islandmagic/bb-link/enclosure/contribs/F4LFJ/BB-Link_case_02.jpeg

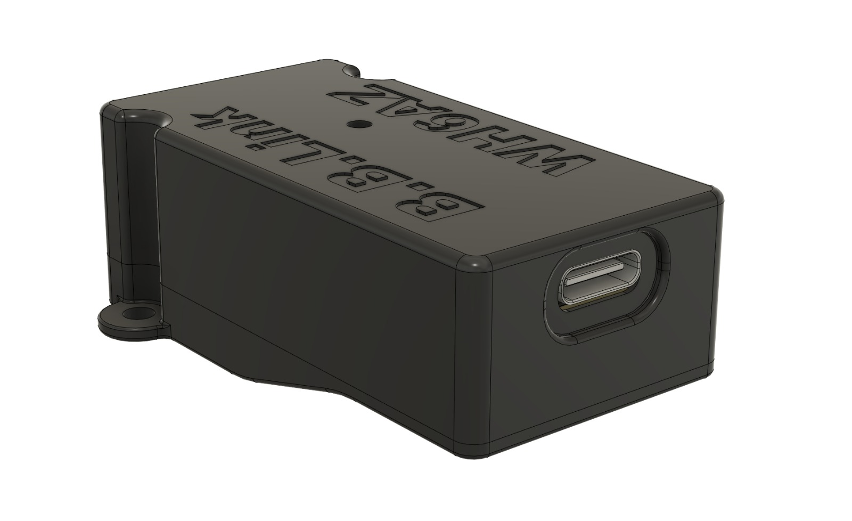
enclosure/contribs/F4LFJ/BB-Link_case_02.jpeg
