islandmagic/bb-link/src/bb-link/Adapter.h

#pragma once
#ifndef ADAPTER_H
#define ADAPTER_H

#include "Arduino.h"

#if defined(ARDUINO_TINYPICO)
#include <TinyPICO.h>
#endif

#include "StatusIndicatorBase.h"
#include "StatusIndicatorDummy.h"
#if defined(ARDUINO_TINYPICO)
#include "StatusIndicator.h"
#endif

#include "TouchButtonBase.h"
#include "TouchButtonDummy.h"
#if defined(ARDUINO_TINYPICO)
#include "TouchButton.h"
#endif

#include "Bridge.h"
#include "FiniteStateMachine.h"

#include <esp_ota_ops.h>

#define CAPACITIVE_TOUCH_INPUT_PIN T0  // Pin 4
#define ADAPTER_NAME "B.B. Link"       // Changing this will prevent RadioMail to know that QSY is supported.

#define FIRMWARE_VERSION_MAJOR 0
#define FIRMWARE_VERSION_MINOR 7
#define FIRMWARE_VERSION_PATCH 8

#define DEVICE_NAMESPACE "bb-link-hw"
#define IDENTITY_KEY "identity"

enum hardware_board_t {
  hardware_board_unknown = 0,
  hardware_board_tinypico = 1,
  hardware_board_pico32 = 2
};

#if defined(ARDUINO_TINYPICO)
#define HARDWARE_BOARD hardware_board_tinypico
#define HARDWARE_VERSION_MAJOR 3
#define HARDWARE_VERSION_MINOR 0
#endif

#if defined(ARDUINO_ESP32_PICO)
#define HARDWARE_BOARD hardware_board_pico32
#define HARDWARE_VERSION_MAJOR 1
#define HARDWARE_VERSION_MINOR 0
#endif

#if !defined(HARDWARE_BOARD)
#error "Unknown hardware board. Please define HARDWARE_BOARD so that OTA updater knows what to do."
#endif

DECLARE_STATE(AdapterState);

enum shutdown_reason_t {
  userInitiated = 0x00,
  idleTimeout = 0x01,
  lowBattery = 0x02
};

class Adapter : public BLECharacteristicCallbacks {
public:
  Adapter();
  void init();
  void perform();
  Bridge bridge;
  String getAdapterName();

private:
#if defined(ARDUINO_TINYPICO)
  TinyPICO tp = TinyPICO();
  StatusIndicator statusIndicator = StatusIndicator(tp);
  TouchButton touchButton = TouchButton(CAPACITIVE_TOUCH_INPUT_PIN);
#else
  StatusIndicatorDummy statusIndicator = StatusIndicatorDummy();
  TouchButtonDummy touchButton = TouchButtonDummy();
#endif

  unsigned long lastBatteryCheck = 0;
  shutdown_reason_t shutdownReason;

  AdapterState idleState;
  AdapterState inUseState;
  AdapterState shutdownState;
  AdapterState showBatteryState;
  AdapterState otaFlashState;
  FSMT<AdapterState> adapterStateMachine;

  BLECharacteristic *pOtaFlash;
  BLECharacteristic *pOtaIdentity;
  esp_ota_handle_t otaHandle = 0;

  void verifyFirmware();
  void onLongPressed();
  void onShortPressed();
  void lowBatteryWatchguard();
  void updateSendReceiveStatus();
  bool isUSBPower();
  void doShutdown();

  void shutdownEnter();
  void shutdownUpdate();
  void shutdownExit();
  void idleEnter();
  void idleUpdate();
  void idleExit();
  void inUseEnter();
  void inUseUpdate();
  void inUseExit();
  void showBatteryEnter();
  void showBatteryUpdate();
  void showBatteryExit();
  void otaFlashEnter();
  void otaFlashUpdate();
  void otaFlashExit();

  void initBLEOtaService();

  void onWrite(BLECharacteristic *pCharacteristic);
  void onRead(BLECharacteristic *pCharacteristic);

  String fetchAdapterName();
};

#endif
